HiramSilvey/HS/controller/main/main.ino

// Copyright 2021 Hiram Silvey

#include <memory>

#include "pins.h"
#include "controller.h"
#include "ns_controller.h"
#include "pc_controller.h"

std::unique_ptr<Controller> controller;
extern uint8_t nsgamepad_active;

void setup() {
  delay(100);

  std::vector<std::unique_ptr<Controller>> controllers;
  if (nsgamepad_active) {
    controllers.push_back(std::make_unique<NSController>());
  } else {
    controllers.push_back(std::make_unique<PCController>());
  }

  while(true) {
    for (auto& c : controllers) {
      if (c->Init()) {
        controller = std::move(c);
        return;
      }
    }
    delay(50);
  }
}

void loop() {
  controller->Loop();
}
