HiramSilvey/HS/controller/main/controller.h

// Copyright 2021 Hiram Silvey

#ifndef CONTROLLER_H_
#define CONTROLLER_H_

#include <memory>

#include "hall_joystick.h"
#include "profile.pb.h"

class Controller {
public:
  // Initializations to be run once before the main loop. Returns true on
  // success, false otherwise.
  virtual bool Init() = 0;

  // Main loop to be run each tick.
  virtual void Loop() = 0;

private:
  // Load the controller profile settings based on the button held.
  virtual void LoadProfile() = 0;
};

#endif  // CONTROLLER_H_
