HiramSilvey/HS/configurator/src/lib.rs

// Copyright 2024 Hiram Silvey

use profile::profile::layer::action::ActionType::{Analog, Digital};
use profile::profile::layer::Action;
use profile::profile::Layer;
use profile::profile::Layout;
use profile::Profile;
use std::fmt;

pub mod encoder;
pub mod profile {
    include!(concat!(env!("OUT_DIR"), "/hs.profile.rs"));
}
pub mod profiles;

impl fmt::Display for Action {
    fn fmt(&self, f: &mut fmt::Formatter<'_>) -> fmt::Result {
        let action_type = match &self.action_type {
            Some(x) => x,
            None => return Err(fmt::Error),
        };
        match action_type {
            Digital(x) => write!(f, "{}", x)?,
            Analog(x) => write!(f, "{}, {}", x.id, x.value)?,
        }
        Ok(())
    }
}

impl fmt::Display for Layer {
    fn fmt(&self, f: &mut fmt::Formatter<'_>) -> fmt::Result {
        let actions = [
            ("thumb top", self.thumb_top.as_ref()),
            ("thumb middle", self.thumb_middle.as_ref()),
            ("thumb bottom", self.thumb_bottom.as_ref()),
            ("index top", self.index_top.as_ref()),
            ("index middle", self.index_middle.as_ref()),
            ("middle top", self.middle_top.as_ref()),
            ("middle middle", self.middle_middle.as_ref()),
            ("middle bottom", self.middle_bottom.as_ref()),
            ("ring top", self.ring_top.as_ref()),
            ("ring middle", self.ring_middle.as_ref()),
            ("ring bottom", self.ring_bottom.as_ref()),
            ("pinky top", self.pinky_top.as_ref()),
            ("pinky middle", self.pinky_middle.as_ref()),
            ("pinky bottom", self.pinky_bottom.as_ref()),
            ("left outer", self.left_outer.as_ref()),
            ("left inner", self.left_inner.as_ref()),
        ];
        for action in actions.iter() {
            if let Some(unwrapped) = action.1 {
                writeln!(f, "\t\t{}: {}", action.0, unwrapped)?;
            } else {
                writeln!(f, "\t\t{}: N/A", action.0)?;
            }
        }
        Ok(())
    }
}

impl fmt::Display for Layout {
    fn fmt(&self, f: &mut fmt::Formatter<'_>) -> fmt::Result {
        let base_layer = match &self.base {
            Some(x) => x,
            None => return Err(fmt::Error),
        };
        writeln!(f, "\tbase: {{\n{}\n\t}}", base_layer)?;
        if let Some(mod_layer) = &self.r#mod {
            writeln!(f, "\tmod: {{\n{}\n\t}}", mod_layer)?;
        }
        Ok(())
    }
}

impl fmt::Display for Profile {
    fn fmt(&self, f: &mut fmt::Formatter<'_>) -> fmt::Result {
        writeln!(f, "{{")?;
        writeln!(f, "\tname: {}", self.name)?;
        for platform_config in &self.platform_config {
            writeln!(f, "\tplatform: {}", platform_config.platform)?;
            writeln!(f, "\tposition: {}", platform_config.position)?;
        }
        let layout = match &self.layout {
            Some(x) => x,
            None => return Err(fmt::Error),
        };
        write!(f, "{}", layout)?;
        writeln!(f, "}}")?;
        Ok(())
    }
}
