HiramSilvey/HS/configurator/src/profiles.rs

// Copyright 2024 Hiram Silvey

use crate::profile::Profile;
use anyhow::Result;
use prost::Message;
use std::fs;
use std::io::Cursor;
use std::path::Path;
use std::vec::Vec;

pub fn load_all(path: &Path) -> Result<Vec<Profile>> {
    let mut profiles = Vec::new();
    for entry in fs::read_dir(path)? {
        let entry = entry?;
        let p = entry.path();
        if p.is_dir() {
            profiles.append(&mut load_all(&p)?);
        } else {
            let buf = fs::read(p)?;
            let profile = Profile::decode(&mut Cursor::new(buf))?;
            profiles.push(profile);
        }
    }
    Ok(profiles)
}

pub fn save_all(profiles: &Vec<Profile>, path: &Path) -> Result<()> {
    for profile in profiles {
        let mut buf = Vec::new();
        buf.reserve(profile.encoded_len());
        profile.encode(&mut buf)?;
        let path = path.join(Path::new(&profile.name));
        fs::write(path, buf)?;
    }
    Ok(())
}

pub fn find(profiles: &Vec<Profile>, name: &str) -> Option<usize> {
    for i in 0..profiles.len() {
        if profiles[i].name == name {
            return Some(i);
        }
    }
    None
}

#[cfg(test)]
mod tests {
    use super::*;

    #[test]
    #[should_panic]
    fn test_load_all_bad_dir() {
        load_all(&Path::new("")).unwrap();
    }
}
