HiramSilvey/HS/main/decoder.h

// Copyright 2024 Hiram Silvey

#ifndef DECODER_H_
#define DECODER_H_

#include <vector>

#include "profile.pb.h"
#include "teensy.h"

namespace hs {
namespace decoder {

namespace internal {

std::vector<hs_profile_Profile_PlatformConfig> DecodeHeader(
    const Teensy& teensy, int addr);
int FetchData(const Teensy& teensy, int remaining, int& addr,
              uint8_t& curr_byte, int& unread);
hs_profile_Profile_Layer DecodeLayer(const Teensy& teensy, int& addr);
hs_profile_Profile_Layout DecodeBody(const Teensy& teensy, int& addr);

}  // namespace internal

hs_profile_Profile_Layout Decode(const Teensy& teensy,
                                 hs_profile_Profile_Platform Platform,
                                 int position);

}  // namespace decoder
}  // namespace hs

#endif  // PROFILES_H_
