HiramSilvey/HS/main/hall_joystick.cpp

// Copyright 2024 Hiram Silvey

#include "hall_joystick.h"

#include <memory>

#include "math.h"
#include "teensy.h"
#include "util.h"

namespace hs {

HallJoystick::HallJoystick(const Teensy& teensy, int min, int max,
			   int threshold)
    : out_({.min = min, .max = max}),
      out_neutral_((max - min + 1) / 2 + min),
      threshold_({threshold * -1, threshold}),
      last_fetch_micros_(0) {
  int neutral_x = util::GetIntFromEEPROM(teensy, 0);
  int neutral_y = util::GetIntFromEEPROM(teensy, 4);
  int range = util::GetIntFromEEPROM(teensy, 8);
  x_in_ = {.min = neutral_x - range, .max = neutral_x + range};
  y_in_ = {.min = neutral_y - range, .max = neutral_y + range};
  int16_t angle_ticks = util::GetShortFromEEPROM(teensy, 12);
  angle_ = (M_PI * angle_ticks) / 2000.0;
  curr_coords_ = {out_neutral_, out_neutral_};
}

int HallJoystick::Normalize(const Teensy& teensy, double val,
			    const Bounds& in) {
  int mapped =
      round(static_cast<double>(val - in.min) /
		static_cast<double>(in.max - in.min) * (out_.max - out_.min) +
	    out_.min);
  return teensy.Constrain(mapped, out_.min, out_.max);
}

int HallJoystick::ResolveDigitalCoord(int coord) {
  const int percent_tilted =
      ((coord - out_neutral_) * 100) / (out_neutral_ - out_.min);
  if (percent_tilted <= threshold_.first) {
    return out_.min;
  }
  if (percent_tilted >= threshold_.second) {
    return out_.max;
  }
  return out_neutral_;
}

HallJoystick::Coordinates HallJoystick::GetCoordinates(Teensy& teensy) {
  if (teensy.Micros() - last_fetch_micros_ < 330) {
    return curr_coords_;
  }

  teensy.UpdateHallData();
  last_fetch_micros_ = teensy.Micros();

  float z = teensy.GetHallZ();
  int x = teensy.GetHallX() / z * 1000000;
  int y = teensy.GetHallY() / z * 1000000;

  // Rotate the coordinates according to the configuration angle. This is a
  // no-op if the angle is 0.
  double rotated_x = x * cos(angle_) + y * sin(angle_);
  double rotated_y = -x * sin(angle_) + y * cos(angle_);

  x = Normalize(teensy, rotated_x, x_in_);
  y = Normalize(teensy, rotated_y, y_in_);

  if (threshold_.first < 0) {
    // DIGITAL
    curr_coords_ = {ResolveDigitalCoord(x), ResolveDigitalCoord(y)};
  } else {
    // ANALOG
    curr_coords_ = {x, y};
  }
  return curr_coords_;
}

int HallJoystick::get_min() { return out_.min; }

int HallJoystick::get_max() { return out_.max; }

int HallJoystick::get_neutral() { return out_neutral_; }

}  // namespace hs
