HiramSilvey/HS/main/pins.cpp

// Copyright 2024 Hiram Silvey

#include "pins.h"

#include "profile.pb.h"

namespace hs {
namespace pins {

std::vector<ActionPin> GetActionPins(const hs_profile_Profile_Layer& layer) {
  return {{layer.thumb_top, kThumbTop},
          {layer.thumb_middle, kThumbMiddle},
          {layer.thumb_bottom, kThumbBottom},
          {layer.index_top, kIndexTop},
          {layer.index_middle, kIndexMiddle},
          {layer.middle_top, kMiddleTop},
          {layer.middle_middle, kMiddleMiddle},
          {layer.middle_bottom, kMiddleBottom},
          {layer.ring_top, kRingTop},
          {layer.ring_middle, kRingMiddle},
          {layer.ring_bottom, kRingBottom},
          {layer.pinky_top, kPinkyTop},
          {layer.pinky_middle, kPinkyMiddle},
          {layer.pinky_bottom, kPinkyBottom},
          {layer.left_outer, kLeftOuter},
          {layer.left_inner, kLeftInner}};
}

}  // namespace pins
}  // namespace hs
