HiramSilvey/HS/main/hall_joystick.cc

// Copyright 2021 Hiram Silvey

#include "main/hall_joystick.h"

#include <Tlv493d.h>

void HallJoystick::Setup() {
  sensor_.begin();
}

int HallJoystick::GetX() {
  // TODO(hiram): implement
  return 0;
}

int HallJoystick::GetY() {
  // TODO(hiram): implement
  return 0;
}
