HiramSilvey/HS/main/test/mock_teensy.h

// Copyright 2024 Hiram Silvey

#ifndef MOCK_TEENSY_H_
#define MOCK_TEENSY_H_

#include "gmock/gmock.h"
#include "teensy.h"

namespace hs {

class MockTeensy : public Teensy {
 public:
  MOCK_METHOD(uint8_t, GetUSBConfiguration, (), (const override));
  MOCK_METHOD(bool, DigitalReadLow, (uint8_t pin), (const override));
  MOCK_METHOD(void, Exit, (int status), (const override));
  MOCK_METHOD(int, Constrain, (int amount, int low, int high),
              (const override));
  MOCK_METHOD(void, SerialWrite, (uint8_t val), (const override));
  MOCK_METHOD(void, SerialWrite, (uint8_t * vals, int size), (const override));
  MOCK_METHOD(int, SerialRead, (), (const override));
  MOCK_METHOD(int, SerialAvailable, (), (const override));
  MOCK_METHOD(unsigned long, Millis, (), (const override));
  MOCK_METHOD(unsigned long, Micros, (), (const override));
  MOCK_METHOD(void, JoystickUseManualSend, (), (const override));
  MOCK_METHOD(void, SetJoystickX, (int val), (const override));
  MOCK_METHOD(void, SetJoystickY, (int val), (const override));
  MOCK_METHOD(void, SetJoystickZ, (int val), (const override));
  MOCK_METHOD(void, SetJoystickZRotate, (int val), (const override));
  MOCK_METHOD(void, SetJoystickSliderLeft, (int val), (const override));
  MOCK_METHOD(void, SetJoystickSliderRight, (int val), (const override));
  MOCK_METHOD(void, SetJoystickButton, (uint8_t pin, bool active),
              (const override));
  MOCK_METHOD(void, SetJoystickHat, (int angle), (const override));
  MOCK_METHOD(void, JoystickSendNow, (), (const override));
  MOCK_METHOD(uint8_t, EEPROMRead, (int addr), (const override));
  MOCK_METHOD(void, EEPROMUpdate, (int addr, uint8_t val), (const override));
  MOCK_METHOD(void, UpdateHallData, (), (override));
  MOCK_METHOD(float, GetHallX, (), (override));
  MOCK_METHOD(float, GetHallY, (), (override));
  MOCK_METHOD(float, GetHallZ, (), (override));
};

}  // namespace hs

#endif  // MOCK_TEENSY_H_
